blakep7/HANDS-EMG/documentation/diagrams/Use-Case.jpg

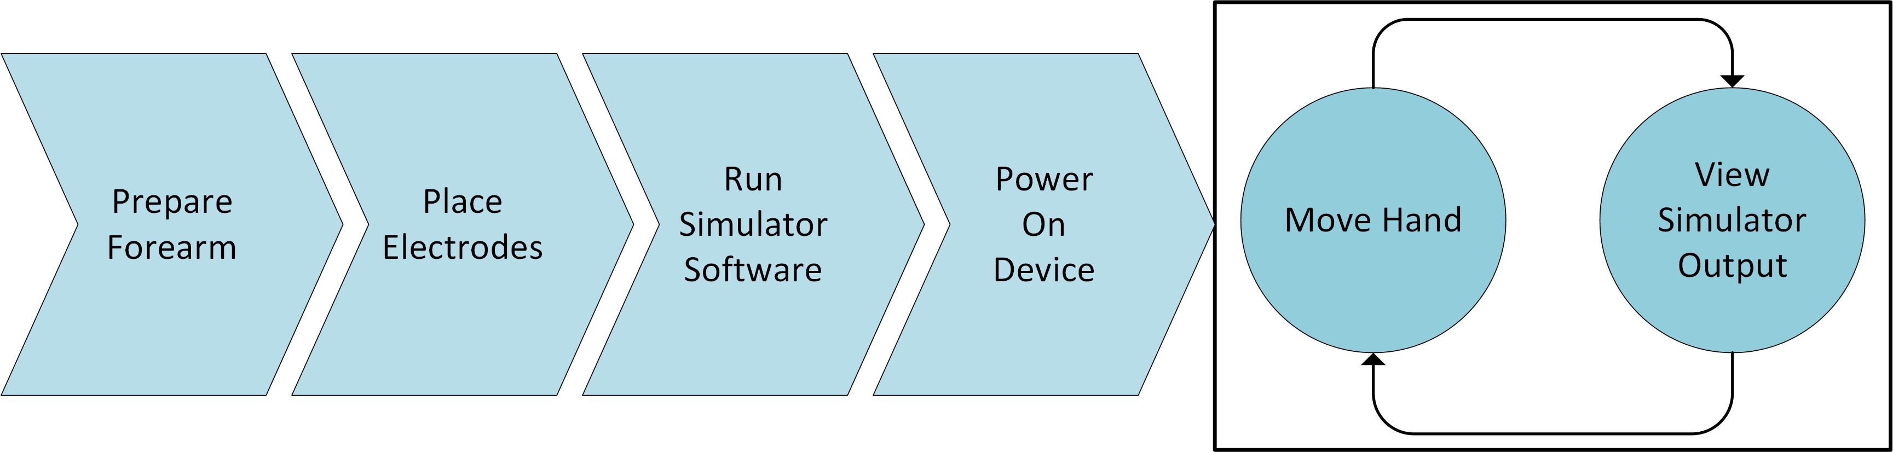
documentation/diagrams/Use-Case.jpg
