blakep7/HANDS-EMG/documentation/diagrams/visio-src/Mechanical-Drawing-front-w-ports.png

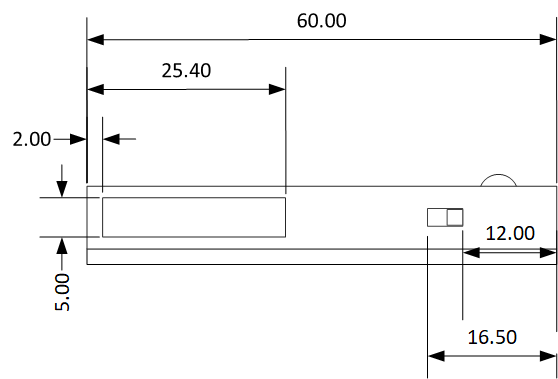
documentation/diagrams/visio-src/Mechanical-Drawing-front-w-ports.png
