blakep7/HANDS-EMG/hardware/phase1/pmic_board/LTC3556_v2.3.jpg

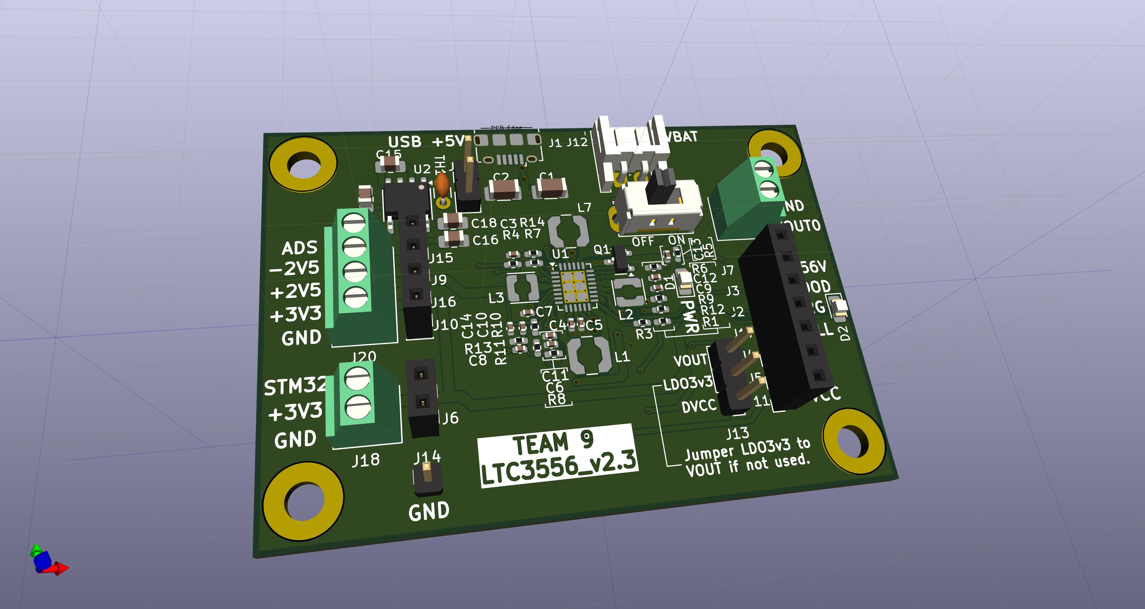
hardware/phase1/pmic_board/LTC3556_v2.3.jpg
