blakep7/HANDS-EMG/software/images/fist-clench.png

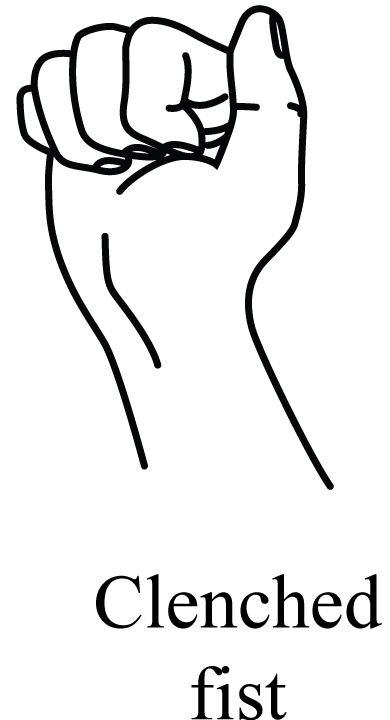
software/images/fist-clench.png
