blakep7/HANDS-EMG/software/images/wrist-extension.png

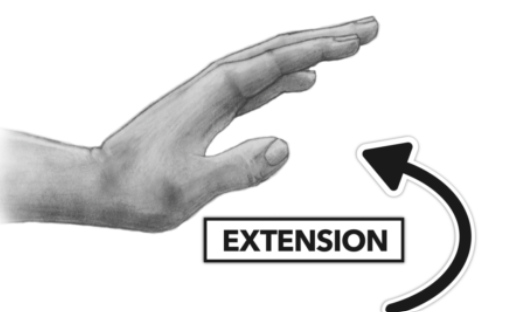
software/images/wrist-extension.png
