blakep7/HANDS-EMG/software/images/wrist-flexion.png

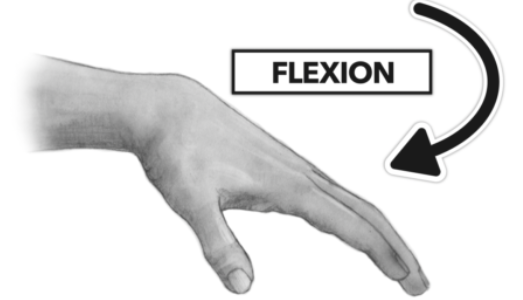
software/images/wrist-flexion.png
