blakep7/HANDS-EMG/hardware/phase1/ads1299_board/ADS1299 Footprints/REG104GA_5/REG104GA-5.step

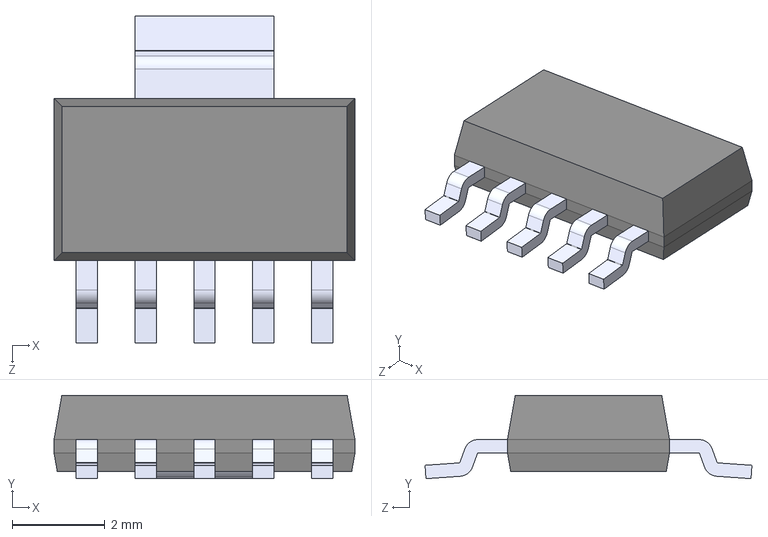
[picture p32: CAD file, 2025-02-27]
hardware/phase1/ads1299_board/ADS1299 Footprints/REG104GA_5/REG104GA-5.step
6.50 x 1.80 x 7.06 mm
