blakep7/HANDS-EMG/hardware/phase1/ads1299_board/ADS1299 Footprints/SSW-105-22-F-D-VS-K/SSW-105-22-F-D-VS-K.step

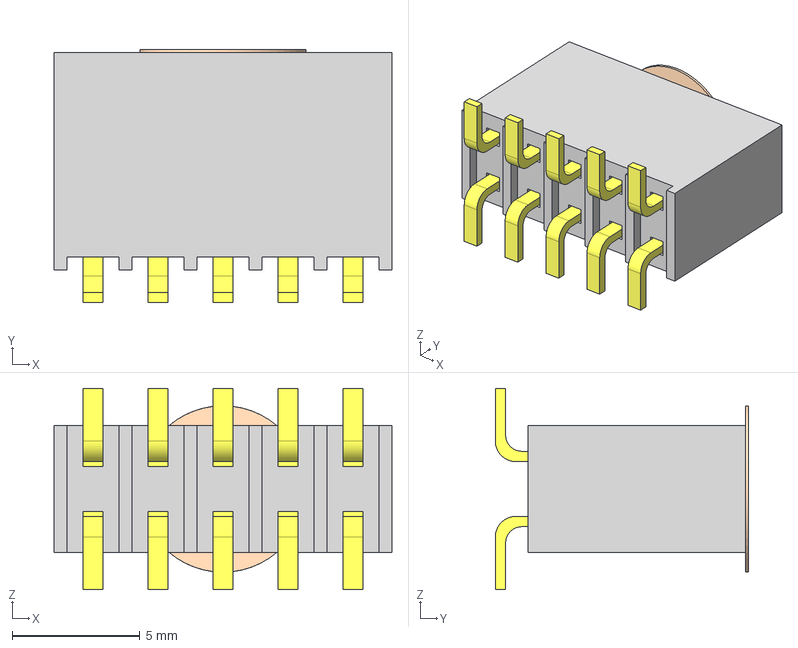
[picture p33: CAD file, 2025-02-27]
hardware/phase1/ads1299_board/ADS1299 Footprints/SSW-105-22-F-D-VS-K/SSW-105-22-F-D-VS-K.step
13.2 x 9.91 x 7.87 mm
T1SSW-105-22-F-D-VS-K
P2SSW-105-22-F-D-VS
