blakep7/HANDS-EMG/hardware/phase1/ads1299_board/ADS1299 Footprints/SSW-118-21-F-D/SSW-118-21-F-D.step

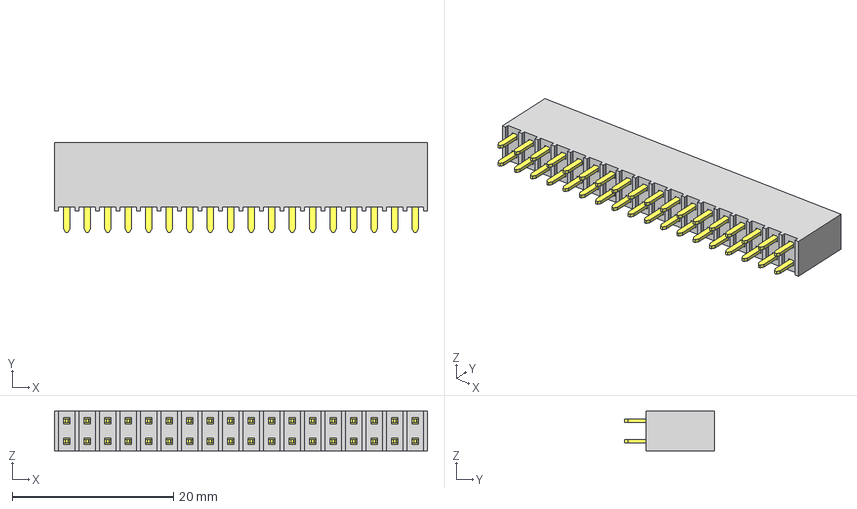
[picture p34: CAD file, 2025-02-27]
hardware/phase1/ads1299_board/ADS1299 Footprints/SSW-118-21-F-D/SSW-118-21-F-D.step
46.2 x 11.2 x 4.95 mm
T1SSW-118-21-F-D
P2SSW-118-21-F-D
