blakep7/HANDS-EMG/hardware/phase1/ads1299_board/ADS1299 Footprints/TSM-110-01-T-DV-P-TR/TSM-110-01-T-DV-P-TR.step

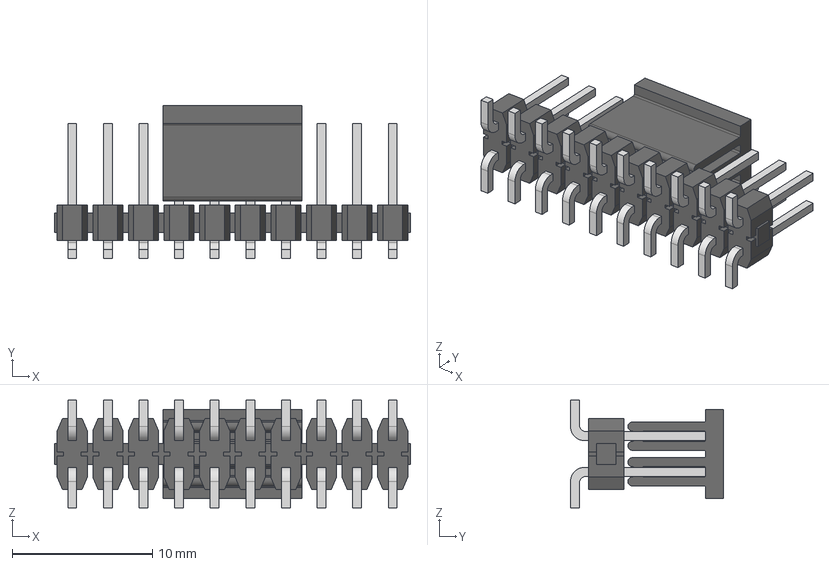
[picture p35: CAD file, 2025-02-27]
hardware/phase1/ads1299_board/ADS1299 Footprints/TSM-110-01-T-DV-P-TR/TSM-110-01-T-DV-P-TR.step
25.4 x 10.9 x 7.70 mm
TSM-110-01-DV_body
PPP-06-01-10--DV
T-1S6-16-T(-01-10-DV)
T-1S6-16-T(-01-10-DV)2
