blakep7/HANDS-EMG/hardware/phase1/ads1299_board/ADS1299 Footprints/TSW-103-07-T-D/TSW-103-07-T-D.step

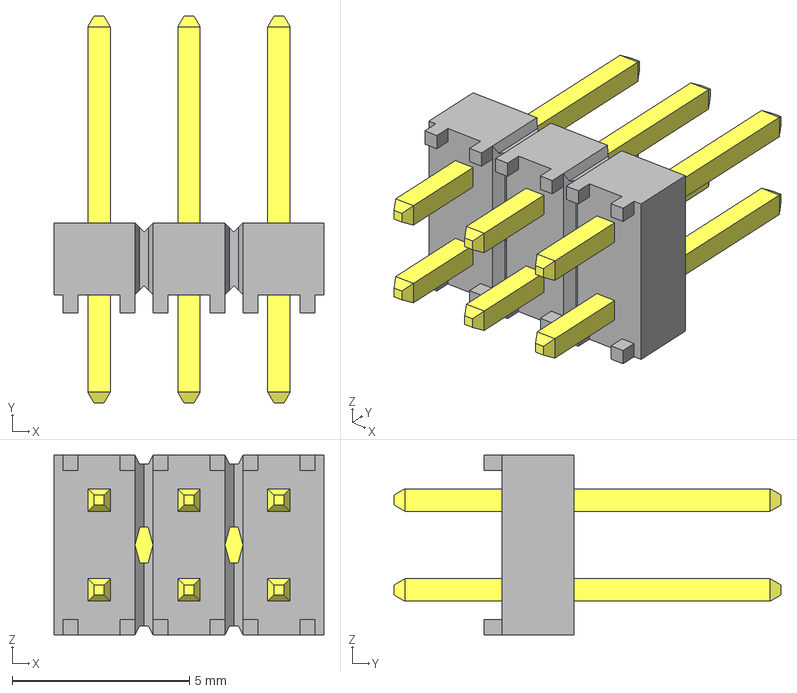
[picture p37: CAD file, 2025-02-27]
hardware/phase1/ads1299_board/ADS1299 Footprints/TSW-103-07-T-D/TSW-103-07-T-D.step
7.62 x 10.9 x 5.08 mm
TSW-103-07-T-D_body
T-1S6-07-TSW-1-07-3-D
