blakep7/HANDS-EMG/hardware/phase1/ads1299_board/ADS1299 Footprints/TSW-103-07-T-S/TSW-103-07-T-S.step

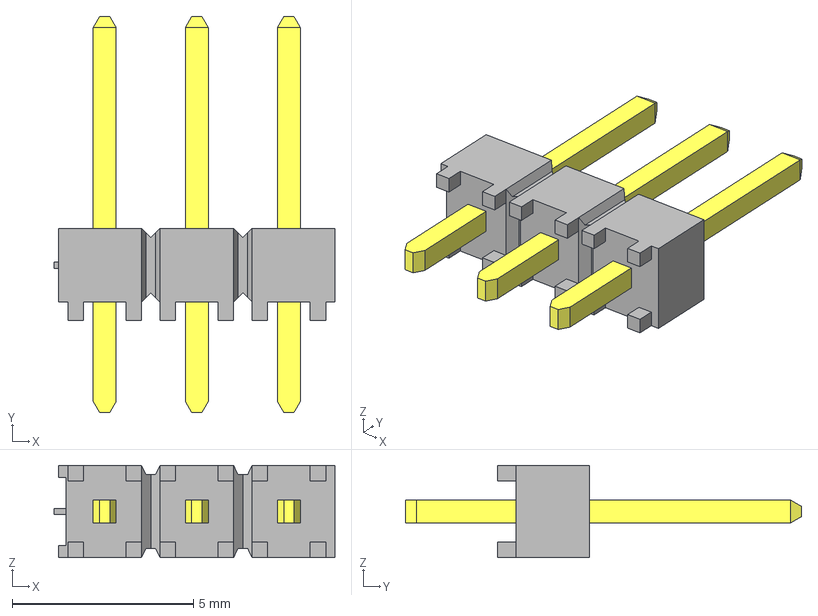
[picture p38: CAD file, 2025-02-27]
hardware/phase1/ads1299_board/ADS1299 Footprints/TSW-103-07-T-S/TSW-103-07-T-S.step
7.75 x 10.9 x 2.54 mm
TSW-103-07-T-S_body
T-1S6-07-TSW-1-07-3-S
