blakep7/HANDS-EMG/documentation/system description and design/integration-rediness-report-pics/custom uC prog test.png

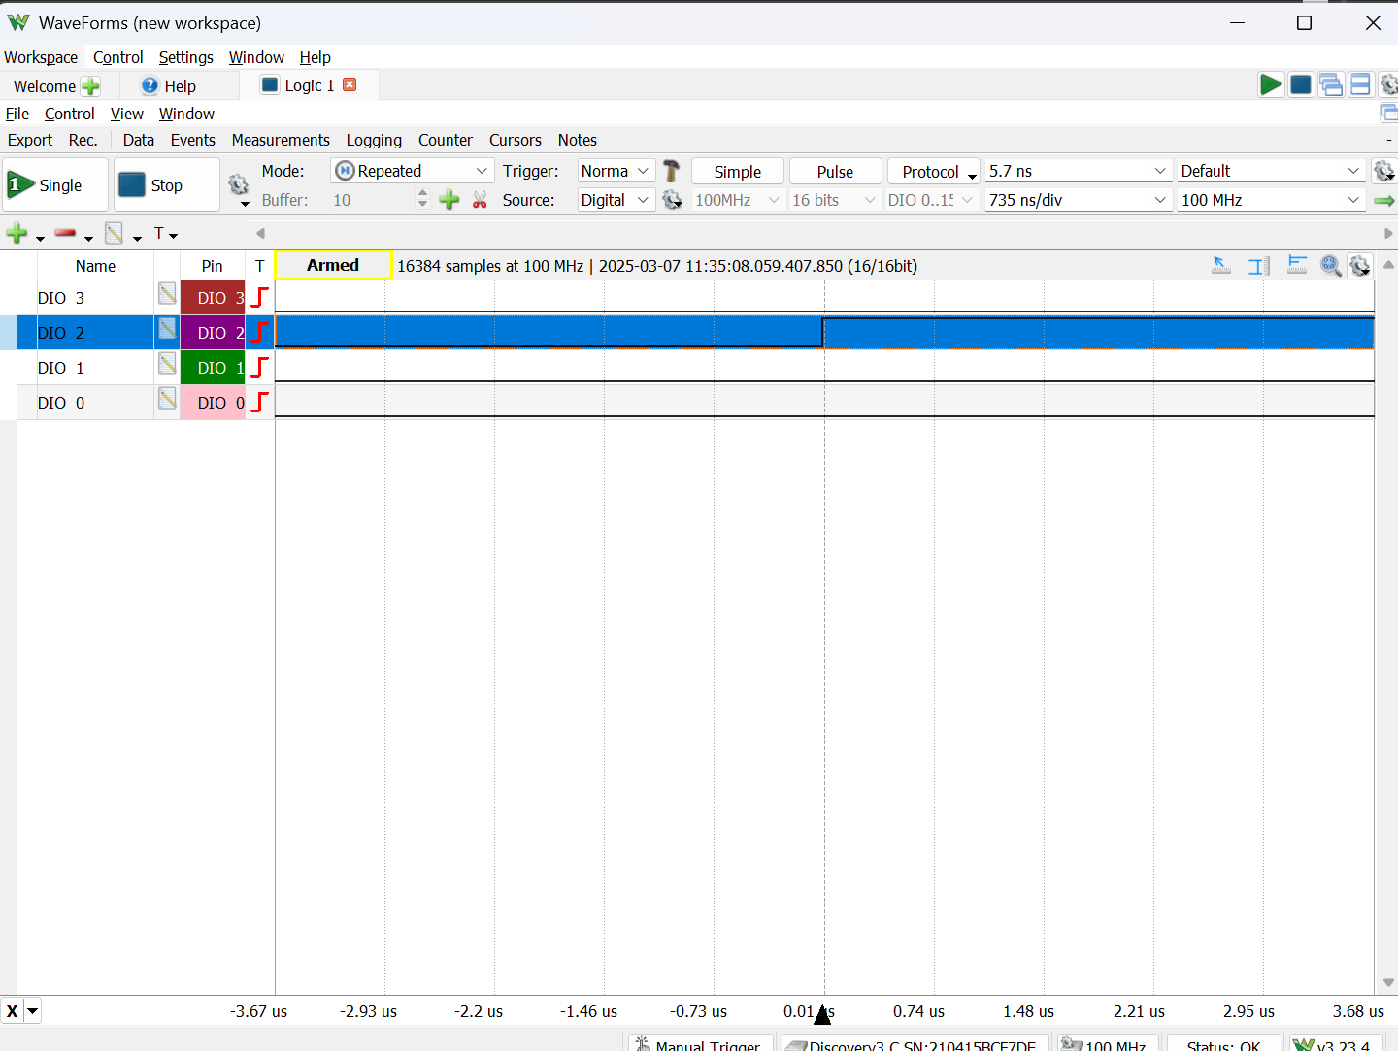
documentation/system description and design/integration-rediness-report-pics/custom uC prog test.png
