blakep7/HANDS-EMG/documentation/system description and design/integration-rediness-report-pics/System-Test.png

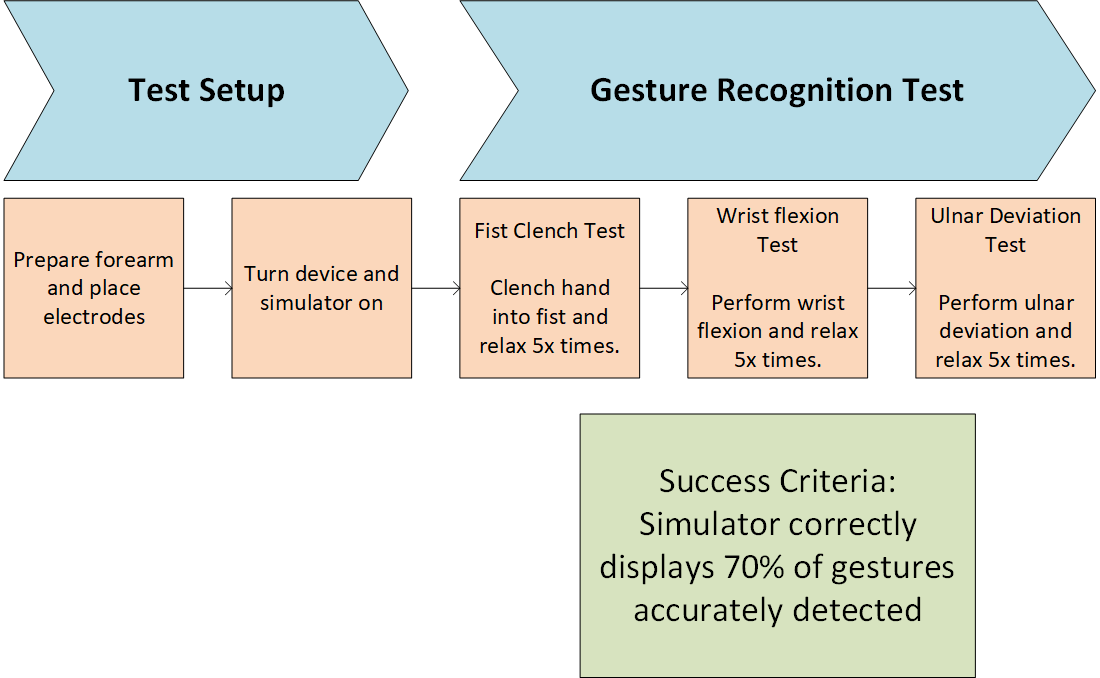
documentation/system description and design/integration-rediness-report-pics/System-Test.png
