blakep7/HANDS-EMG/documentation/system description and design/integration-test-report-pics/ML_confusion_matrix.png

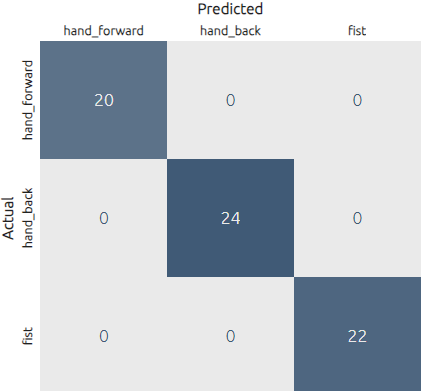
documentation/system description and design/integration-test-report-pics/ML_confusion_matrix.png
