blakep7/HANDS-EMG/documentation/system description and design/integration-test-report-pics/ML_stats.png

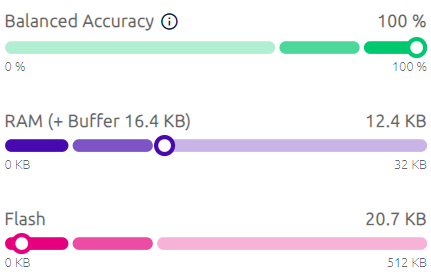
documentation/system description and design/integration-test-report-pics/ML_stats.png
