blakep7/HANDS-EMG/documentation/system description and design/integration-test-report-pics/ML_validation_results.png

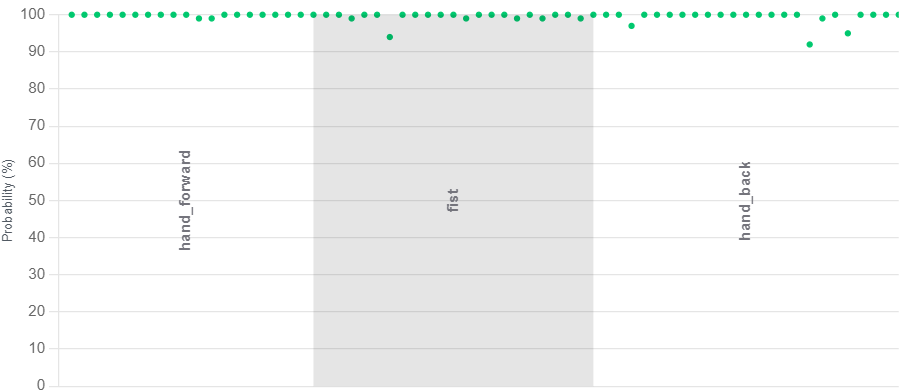
documentation/system description and design/integration-test-report-pics/ML_validation_results.png
